Mango-kid/maciot/images/sch_led.png

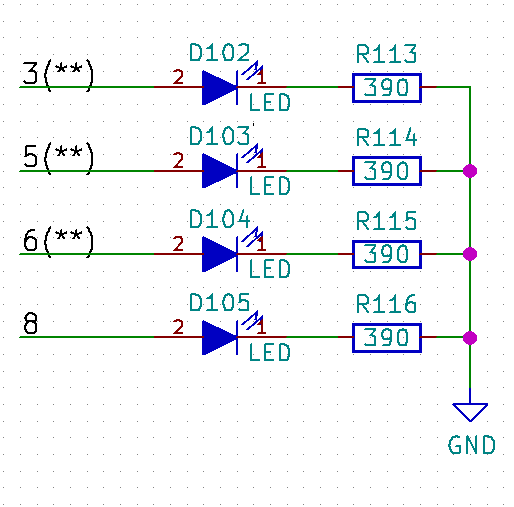
images/sch_led.png
