Mango-kid/maciot/images/sch_power.png

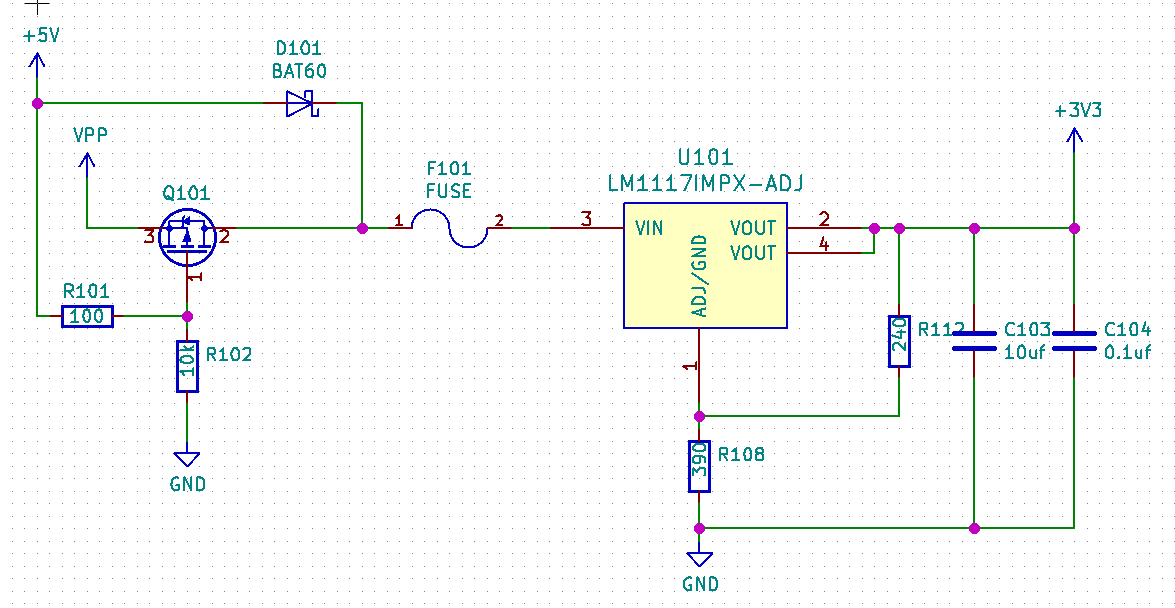
images/sch_power.png
