Mango-kid/maciot/images/sch_usb.png

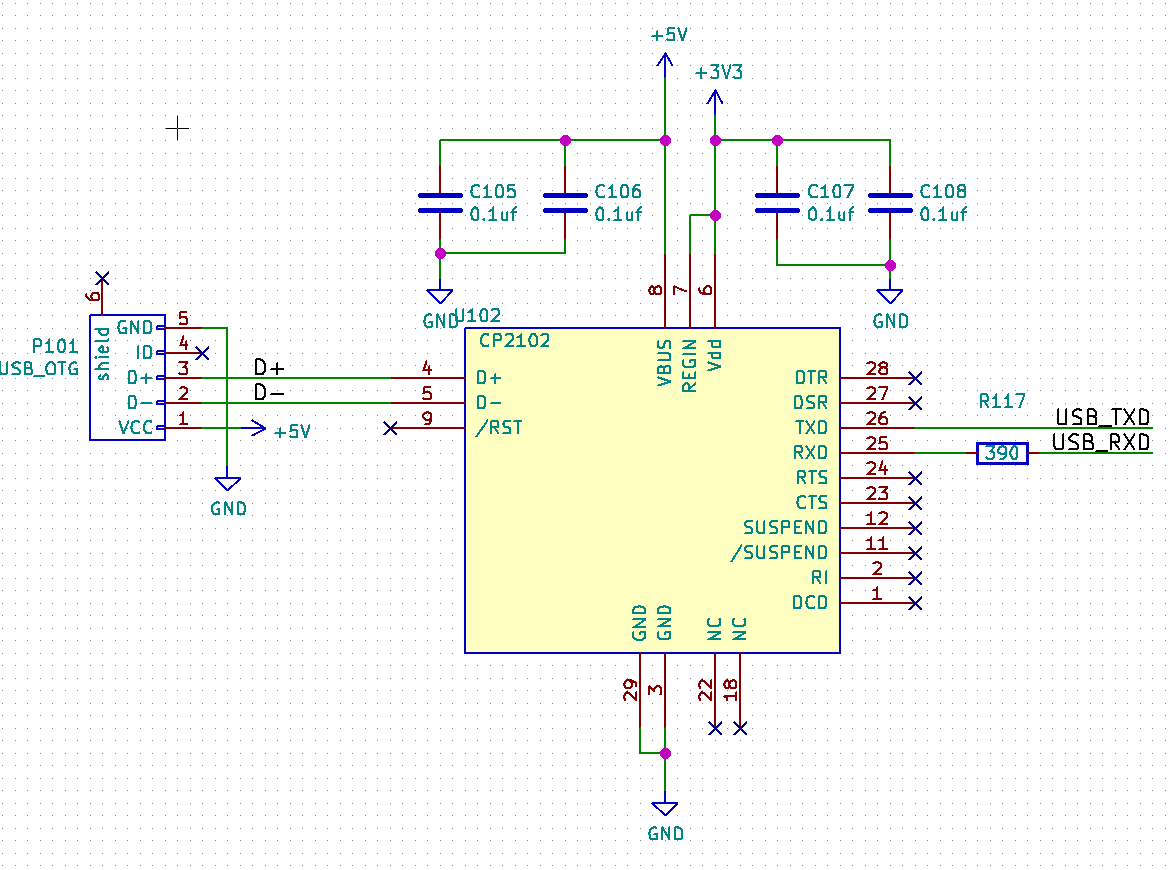
images/sch_usb.png
