Mango-kid/maciot/images/board_setup.png

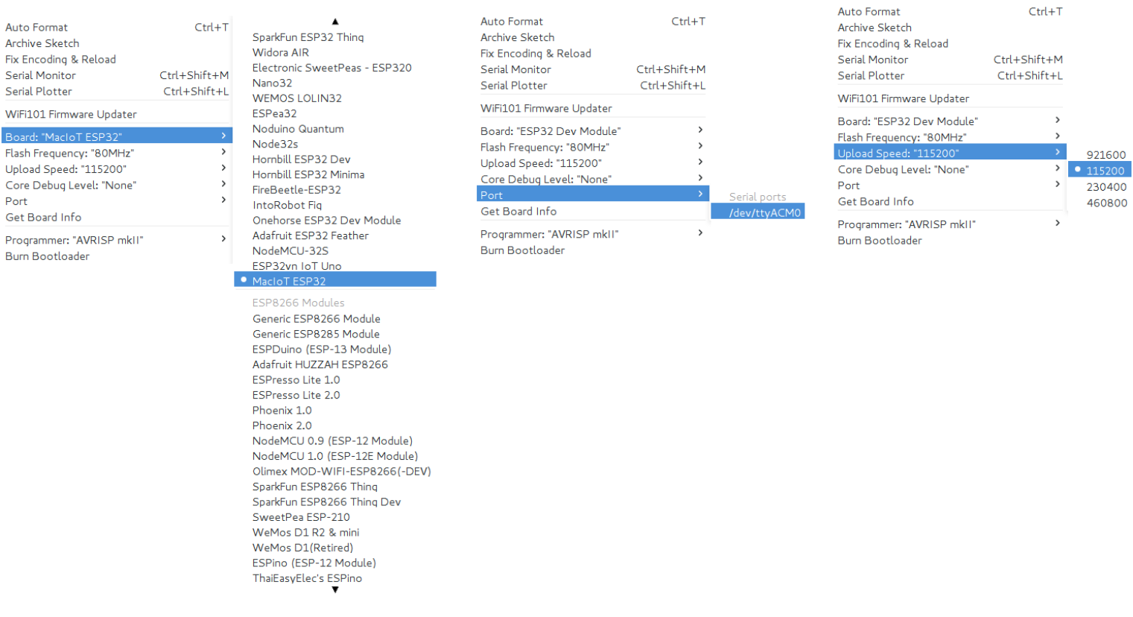
images/board_setup.png
